ronnymajani/project-ding-dong/code/constants.py

INT_PIN = 14
PIN_LED_STATUS = 5
PIN_LED_ERROR = 4

DOORBELL_MESSAGE = "Knock Knock"

WIFI_TIMEOUT = 60
# Time to keep the system on before going into deepsleep when an error occurrs
ERROR_PRE_SLEEP_TIME = 5
# Time to sleep before restarting the system upon an unkown error
ERROR_SLEEP_TIME = 60
# Time to sleep before restarting the system when the device fails to connect to the wifi
WIFI_ERROR_SLEEP_TIME = 1800  # 30 minutes
